Element2424/Pico-Switch-Controller/Images/20250222_210814.jpg

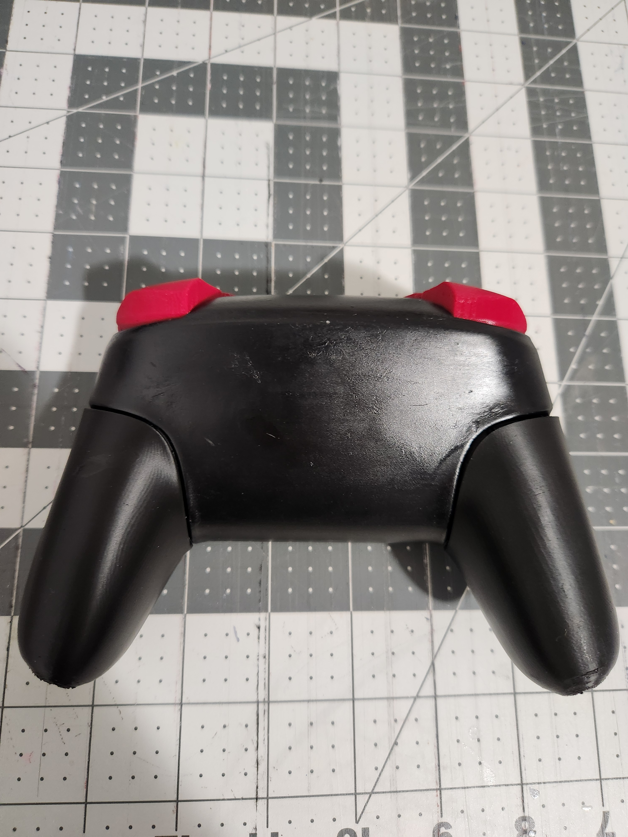
Images/20250222_210814.jpg
