Element2424/Pico-Switch-Controller/Images/20250222_210913.jpg

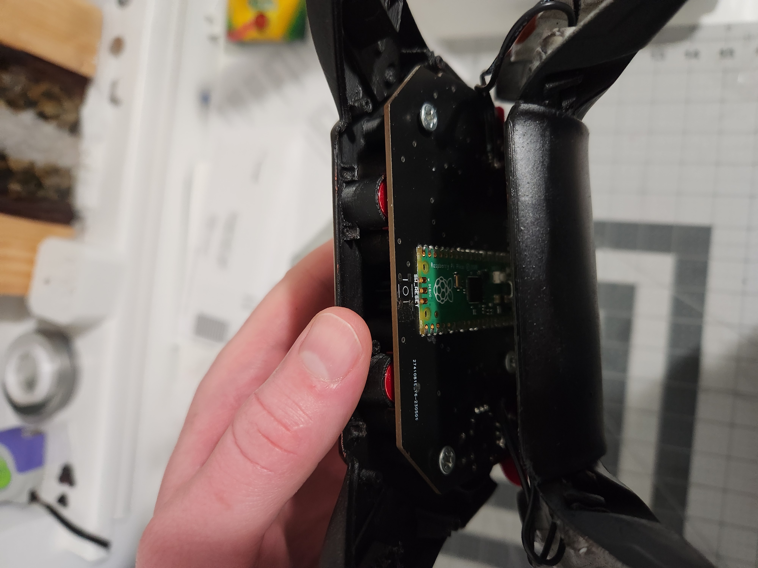
Images/20250222_210913.jpg
