Element2424/Pico-Switch-Controller/Images/20250222_211028.jpg

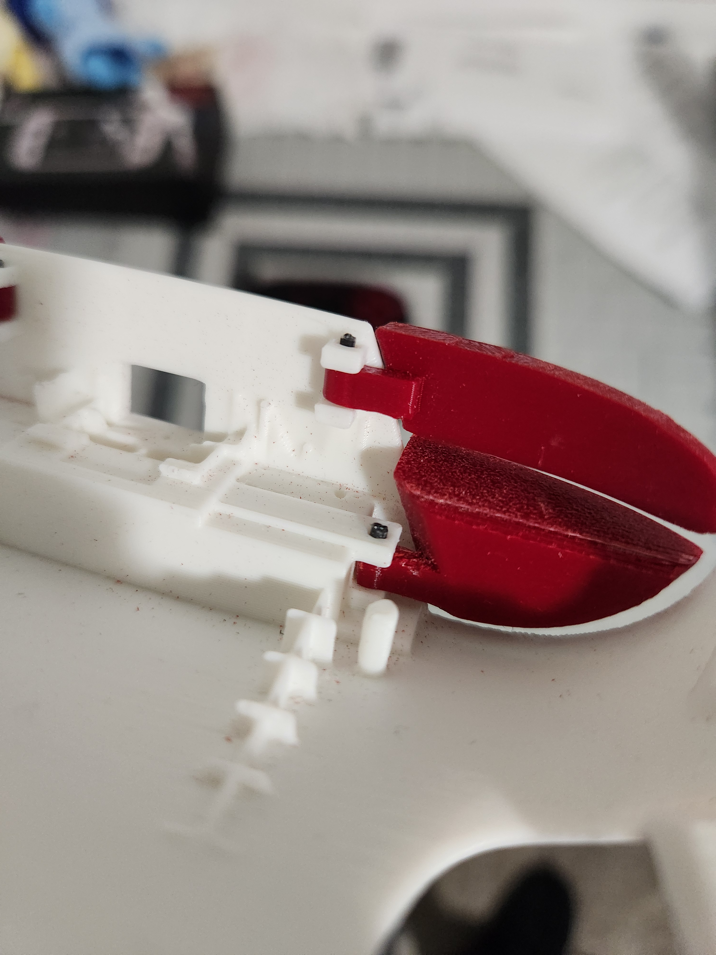
Images/20250222_211028.jpg
