Element2424/Pico-Switch-Controller/Ref/3.png

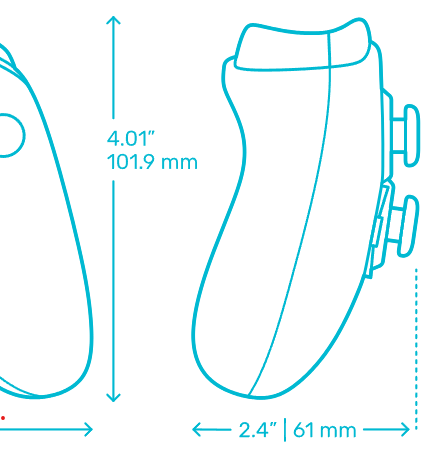
Ref/3.png
