Element2424/Pico-Switch-Controller/Ref/4.png

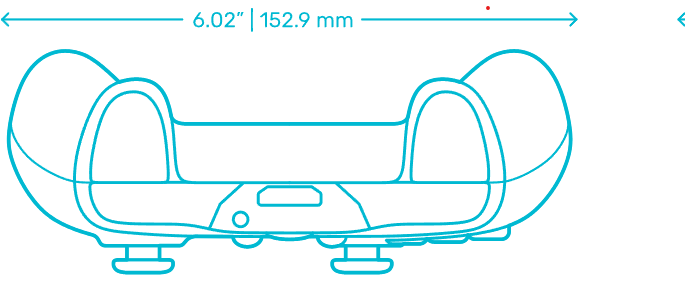
Ref/4.png
