Element2424/Pico-Switch-Controller/Ref/Screenshot 2023-06-17 092402.png

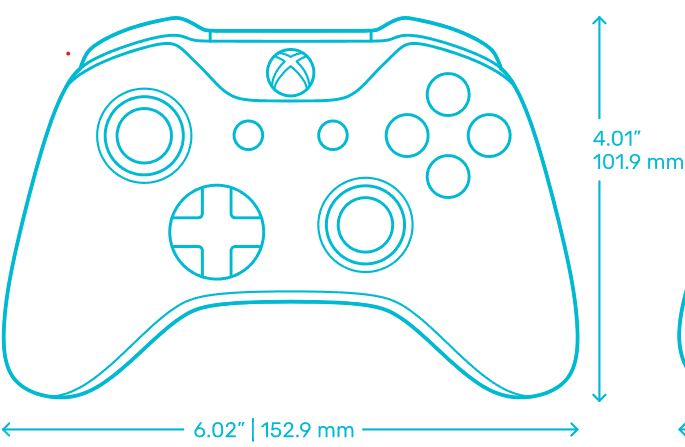
Ref/Screenshot 2023-06-17 092402.png
